bablokb/pcb-pico-datalogger/docs/pcb-datalogger-v2-2.jpg

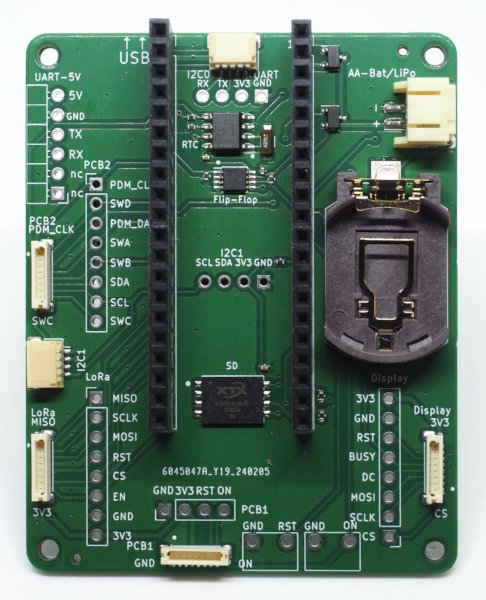
docs/pcb-datalogger-v2-2.jpg
