bablokb/pcb-pico-datalogger/docs/slim-case-v1-back.jpg

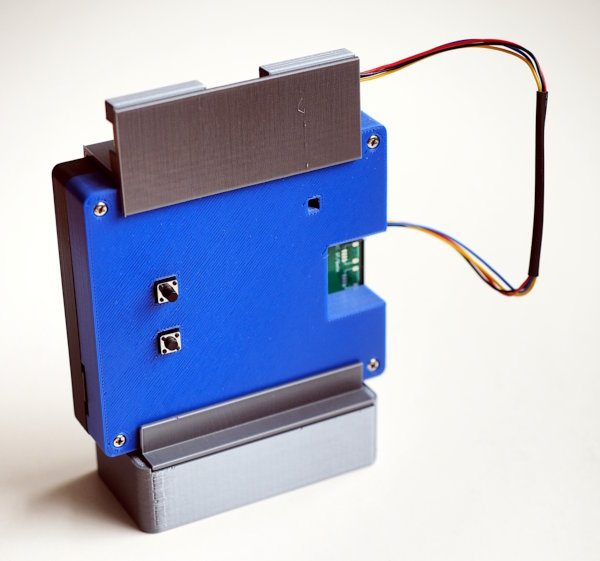
docs/slim-case-v1-back.jpg
