bablokb/pcb-pico-datalogger/docs/slim-case-v1-front.jpg

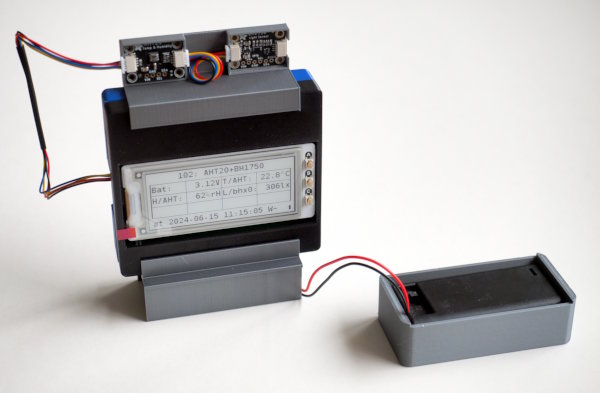
docs/slim-case-v1-front.jpg
