bablokb/pcb-pico-datalogger/lora-pcb.kicad/pcb-3D-top-JLCPCB.png

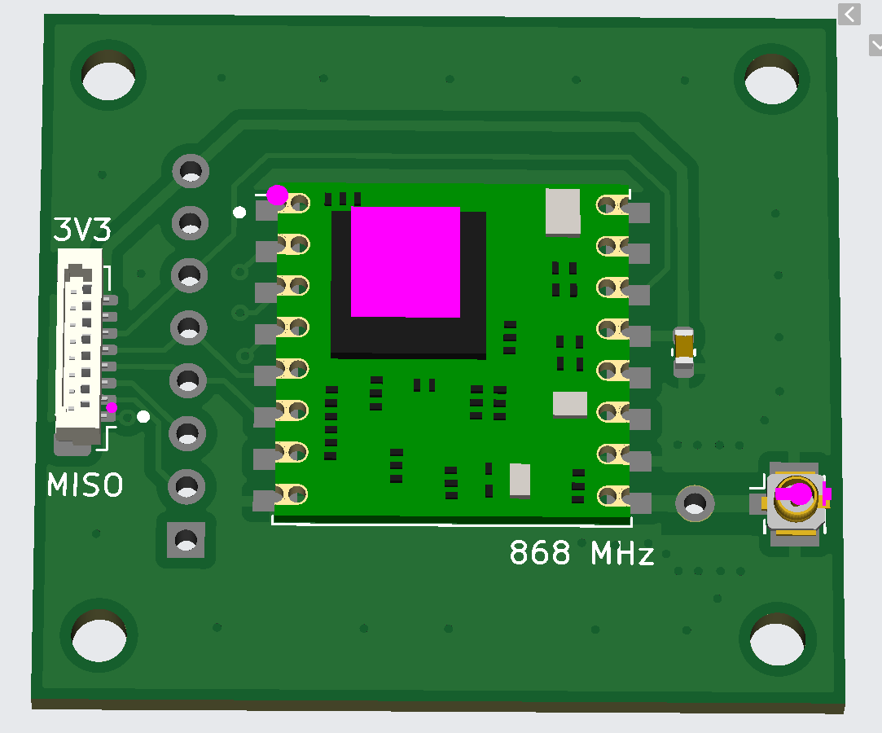
lora-pcb.kicad/pcb-3D-top-JLCPCB.png
