bablokb/pcb-pico-datalogger/src.shared/lora.py

#-----------------------------------------------------------------------------
# Setup of LoRa (adafruit_rfm9x.py). This class also encapsulates the
# data-protocol used by the dataloggers and gateway.
#
# Author: Bernhard Bablok
#
# Website: https://github.com/pcb-pico-datalogger
#-----------------------------------------------------------------------------

from log_writer import Logger
g_logger = Logger()

from singleton import singleton

from digitalio import DigitalInOut, Direction, Pull
import struct
import time
import adafruit_rfm9x
import pins

# --- quality of service settings   ------------------------------------------

# tuple of spreading-factor, coding-rate, signal-bandwidth
# Time per symbol is T(s) = 2**SF/BW
_LORA_QOS = [
  ( 7, 5, 125000),      # 0
  ( 7, 7, 125000),      # 1
  ( 8, 7, 125000),      # 2, default
  ( 9, 7, 125000),      # 3
  (10, 5, 125000),      # 4
  (11, 5, 125000),      # 5
  (11, 8, 125000),      # 6
  (12, 6, 125000),      # 7
  ]
_LORA_QOS_DEF = 2  # 0 is library default

# --- helper class for LoRa   ------------------------------------------------

@singleton
class LORA:
  def __init__(self,config,spi):
    """ constructor """

    # Calling the constructor with None will return the singleton, if it
    # exists. If not, bail out: the app has to retry and provide all arguments.
    if config is None:
      raise ValueError("config is None")

    self._config = config
    self._trace = getattr(config,'LORA_TRACE',False)

    # technical settings (QOS-setting with possible overrides)
    qos  = getattr(config, 'LORA_QOS', _LORA_QOS_DEF)
    sf   = getattr(config, 'LORA_SF', _LORA_QOS[qos][0])
    cr   = getattr(config, 'LORA_CR', _LORA_QOS[qos][1])
    bw   = getattr(config, 'LORA_BW', _LORA_QOS[qos][2])
    g_logger.print(f"LoRa: QOS-parameter: {(sf,cr,bw)}")

    # calculate expected app-level byte-rate: R(B) = sf*(4/cr)*bw/2**sf/8
    self._byte_rate = sf*4/cr*bw/(1<<(sf+3))
    g_logger.print(f"LoRa: expected byte-rate: {self._byte_rate:0.1f} B/s")

    if hasattr(pins,'PIN_LORA_EN'):
      g_logger.print("LoRa: enabling rfm9x")
      pin_enable = DigitalInOut(pins.PIN_LORA_EN)
      pin_enable.direction  = Direction.OUTPUT
      pin_enable.value = 1

    g_logger.print("LoRa: initializing rfm9x")
    pin_cs     = DigitalInOut(pins.PIN_LORA_CS)
    pin_reset  = DigitalInOut(pins.PIN_LORA_RST)
    self.rfm9x = adafruit_rfm9x.RFM9x(
      spi, pin_cs,pin_reset,config.LORA_FREQ,baudrate=100000)

    g_logger.print("LoRa: configuring rfm9x")
    self.rfm9x.spreading_factor = sf
    self.rfm9x.coding_rate      = cr
    self.rfm9x.signal_bandwidth = bw
    if (cr/4)* 1000 / (bw/(1 << sf)) > 16:
      self.rfm9x.low_datarate_optimize = 1
    else:
      self.rfm9x.low_datarate_optimize = 0

    self.rfm9x.enable_crc = True
    self.rfm9x.receive_timeout = getattr(config,'LORA_RECEIVE_TIMEOUT',5.0)
    self.rfm9x.tx_power = getattr(config,"LORA_TX_POWER",13)
    self.rfm9x.node = config.LORA_NODE_ADDR                      # this
    self.rfm9x.destination = getattr(config,"LORA_BASE_ADDR",0)  # gateway
    self.rfm9x.sleep()

  # --- trace LoRa-events   --------------------------------------------------

  def trace(self,msg):
    """ trace LoRa events """
    if self._trace:
      g_logger.print(msg)

  # --- transmit command   ---------------------------------------------------

  def transmit(self,data,msg_type=None,keep_listening=False):
    """ send data """
    if data is None or isinstance(data,str):
      if msg_type and data:
        payload = f"{msg_type},{data}"
      elif msg_type:
        payload = msg_type
      else:
        payload = data
      payload = bytes(payload, "UTF-8")
    else:
      # binary data has no message-type
      payload = data
    self.rfm9x.xmit_timeout = 2 + (len(payload)+4)/self._byte_rate
    if self._trace:
      g_logger.print(f"LoRa: sending data: {payload}")
      g_logger.print(f"LoRa:   xmit_timeout: {self.rfm9x.xmit_timeout: 0.1f}")
      start = time.monotonic()
    rc = self.rfm9x.send(payload,keep_listening=keep_listening)
    if self._trace:
      g_logger.print(f"LoRa:   elapsed: {time.monotonic()-start:0.3f}s")
    return rc

  # --- receive command   ----------------------------------------------------

  def receive(self, decode=True, keep_listening=True, timeout=None):
    """ receive and decode data """
    if self._trace:
      g_logger.print("LoRa: receiving data...")
      start = time.monotonic()
    packet = self.rfm9x.receive(with_header=True,
                                keep_listening=keep_listening,
                                timeout=timeout)
    if self._trace:
      g_logger.print(f"LoRa:   elapsed: {time.monotonic()-start:0.3f}s")
    if packet is None:
      self.trace(
        f"LoRa: no packet within {timeout if timeout else self.rfm9x.receive_timeout:5.2}s")
      return (None,None,None,None)
    else:
      header  = packet[:4]
      if decode:
        try:
          payload = packet[4:].decode()
        except Exception as ex:
          g_logger.print(f"exception while decoding packet: {ex}")
          return (None,None,None,None)
      else:
        payload = packet[4:]
      self.trace(f"LoRa: header: {header}")
      self.trace(f"LoRa: payload: {payload}")
      return (payload,int(header[1]),self.rfm9x.last_snr,self.rfm9x.last_rssi)

  # --- set destination   ----------------------------------------------------

  def set_destination(self,dest):
    """ set destination for transmit """
    self.rfm9x.destination = dest

  # --- broadcast a packet and wait for response   ---------------------------

  def broadcast(self,nr):
    """ send a broadcast packet to the gateway """

    # convert time (int) to compact hex-repr
    ts = time.time()
    ts_str =''.join([hex(b)[-2:] for b in struct.pack("i",ts)])

    # send packet ("B",TS,ID,nr)
    g_logger.print(f"LoRa: broadcast packet {nr}: sending at {ts}")
    start = time.monotonic()
    if self.transmit(
      f"{ts_str},{self._config.LOGGER_ID},{nr}", msg_type="B",
      keep_listening=True):
      duration = time.monotonic()-start
      g_logger.print(f"LoRa: broadcast: packet {nr}: transfer-time: {duration}s")
    else:
      g_logger.print(f"LoRa: broadcast: packet {nr}: failed")
      return None

    # wait for response
    return self.receive(keep_listening=False)

  # --- query time   ---------------------------------------------------------

  def get_time(self,retries=3):
    """ send a time-query packet to the gateway """

    for i in range(retries):
       # send packet ("T")
       g_logger.print(f"LoRa: sending time-query packet, retry={i}")
       start = time.monotonic()
       if self.transmit(None, msg_type="T", keep_listening=True):
         duration = time.monotonic()-start
         g_logger.print(f"LoRa: time-query {i} sent in {duration}s")
       else:
         g_logger.print(f"LoRa: : time-query {i} failed")
         continue

       # wait for response (binary)
       new_time = self.receive(decode=False, keep_listening=False)[0]
       if new_time:
         new_time,*_ = struct.unpack("i", new_time)
         g_logger.print(f"LoRa: : time-query {i} returned {new_time}")
         return new_time
    # query failed!
    g_logger.print(f"LoRa: time-query failed after {retries} retries")
    return None

  # --- send S-message   -----------------------------------------------------

  def send_single(self, data):
    """ send a single-line packet to the gateway """

    content_length = len(data)
    g_logger.print(f"LoRa: sending S-msg, length: {content_length}")
    if self.transmit(data, msg_type="S"):
      resp = self.receive(keep_listening=False, decode=False)
      if resp[0] and int.from_bytes(resp[0]) == content_length:
        g_logger.print("LoRa: ... successful")
        return True
      else:
        g_logger.print(f"LoRa: ... receive failed: response: {resp}")
        return False
    else:
      g_logger.print(f"LoRa: ... transmit failed")
      return False
