bablokb/pcb-pico-datalogger/src.shared/hw_helper.py

#-----------------------------------------------------------------------------
# Module with helper functions to setup the hardware. This module is
# reused by datacollector.py, admin.py, broadcast.py and gateway.py.
#
# Author: Bernhard Bablok
#
# Website: https://github.com/pcb-pico-datalogger
#-----------------------------------------------------------------------------

import atexit
import busio
import displayio
import sdcardio
import storage

from rtc_ext.ext_base import ExtBase

# --- atexit processing   ----------------------------------------------------

def at_exit_spi(spi,logger):
  """ release spi """
  try:
    # may fail if we want to log to SD
    logger.print(f"releasing {spi}")
  except:
    print(f"releasing {spi}")
  spi.deinit()

def at_exit_i2c(i2c,logger):
  """ release i2c-busses """
  try:
    # may fail if we want to log to SD
    logger.print(f"releasing {i2c}")
  except:
    print(f"releasing {i2c}")
  for bus in reversed(i2c):
    try:
      bus.deinit()
    except:
      pass

# --- initialize I2C-busses   ----------------------------------------------

def init_i2c(pins,config,logger):
  """ create and return list of I2C-busses """

  # Standard busses 0 and 1. Bus 0 is shared with UART, so we check
  # the configuration before creating it.
  try:
    i2c = [None,busio.I2C(pins.PIN_SCL1,pins.PIN_SDA1)]
    logger.print(f"created i2c1")
  except Exception as ex:
    logger.print(f"could not create i2c1: {ex}")
    i2c = [None,None]
  if config.HAVE_I2C0:
    try:
      i2c[0] = busio.I2C(pins.PIN_SCL0,pins.PIN_SDA0)
      logger.print(f"created i2c0")
    except:
      logger.print("could not create i2c0 although configured, check wiring!")

  # create busses behind a multiplexer
  if config.HAVE_I2C_MP:
    import adafruit_tca9548a
    for spec in config.HAVE_I2C_MP.split():
      name,loc = spec.rstrip(')').split('(')
      try:
        bus,addr = loc.split(',')
      except:
        bus = loc
        addr = '0x70'
      bus = i2c[int(bus)]
      addr = int(addr,16)
      if name[-2:] == '46' or name[-3:] == '46A':
        i2c_mp = adafruit_tca9548a.PCA9546A(bus,addr)
      else:
        i2c_mp = adafruit_tca9548a.TCA9548A(bus,addr)
      logger.print(f"adding {len(i2c_mp)} I2C-busses from {name}")
      for i2cbus in i2c_mp:
        i2c.append(i2cbus)

  # return result
  atexit.register(at_exit_i2c,i2c,logger)
  return i2c

# --- initialize SD-card   ---------------------------------------------------

def init_sd(pins,config,logger):
  """ initialize SD-card and return SPI-object """

  spi = None
  if config.HAVE_SD:
    try:
      spi    = busio.SPI(pins.PIN_SD_SCK,pins.PIN_SD_MOSI,pins.PIN_SD_MISO)
      sdcard = sdcardio.SDCard(spi,pins.PIN_SD_CS,1_000_000)
      vfs    = storage.VfsFat(sdcard)
      storage.mount(vfs, "/sd")
      logger.print("SD-card mounted on /sd")
      atexit.register(at_exit_spi,spi,logger)
    except Exception as ex:
      if spi:
        spi.deinit()
      raise
  return spi

# --- initialize RTC   -------------------------------------------------------

def init_rtc(pins,config,i2c):
  """ initialize RTC and return RTC-object """

  if config.HAVE_RTC:
    rtc_spec = config.HAVE_RTC.split('(')
    rtc_name = rtc_spec[0]
    rtc_bus  = int(rtc_spec[1][0])
  else:
    rtc_name = None
    rtc_bus  = 0

  # don't care about exceptions, must be handled by caller
  rtc = ExtBase.create(rtc_name,i2c[rtc_bus],net_update=config.NET_UPDATE)
  if rtc_name == "PCF8523":
    if pins.PCB_VERSION > 0:
      rtc.rtc_ext.high_capacitance = True  # uses a 12.5pF capacitor
    if config.HAVE_LIPO:
      rtc.rtc_ext.power_managment = 0b001  # direct switchover Vdd<Vbat
    else:
      rtc.rtc_ext.power_managment = 0b000  # Vdd<Vbat and Vdd < Vth
  return rtc

# --- initialize OLED   ------------------------------------------------------

def init_oled(i2c,config,logger):
  """ init OLED display """

  if config.HAVE_OLED:
    try:
      from oled import OLED
      odisp = OLED(config,i2c,logger)
      display = odisp.get_display()
      logger.print(
        f"OLED created with size {display.width}x{display.height}")
      return odisp
    except Exception as ex:
      logger.print(f"could not initialize OLED: {ex}")
      raise
  return None
