bablokb/pcb-pico-datalogger/src.shared/safemode.py

#-----------------------------------------------------------------------------
# Handle fatal exceptions.
#
# Author: Bernhard Bablok
#
# Website: https://github.com/pcb-pico-datalogger
#-----------------------------------------------------------------------------

import time
import board
import storage
import supervisor
import microcontroller
import pins
import hw_helper

from log_writer import Logger
g_logger = Logger('/sd/safemode.log')

try:
  import config
  TEST_MODE = config.TEST_MODE
except:
  TEST_MODE = False

# --- configure hardware   ---------------------------------------------------

if not hw_helper.init_sd(pins,config,g_logger):
  # no way to log anything, just reset
  microcontroller.reset()

try:
  i2c = hw_helper.init_i2c(pins,config,g_logger)
  the_rtc = hw_helper.init_rtc(pins,config,i2c)
  ts = the_rtc.print_ts(the_rtc.rtc_ext.datetime)
except:
  ts = "???"

reason = (f"{supervisor.runtime.safe_mode_reason}").split(".")[-1]
g_logger.print(f"safemode at {ts} with reason: {reason}")
microcontroller.reset()
