bablokb/pcb-pico-datalogger/src.shared/log_writer.py

#-----------------------------------------------------------------------------
# This class implements a singleton for logging. The constructor takes
# a single argument:
#
#   - None: don't print logmessages
#   - 'console': use normal print-statements for logging
#   - logfile: log to logfile 
#   - uart: an uart-object to receive the log statements
#   - in case of exceptions the latter two fall back to normal print output
#
# Note: this is a singleton, i.e. the logger is only configured the
#       very first time the constructor is called. This should be done
#       early in the (main) program.
#
# Author: Bernhard Bablok
#
# Website: https://github.com/pcb-pico-datalogger
#-----------------------------------------------------------------------------

import time
import supervisor
from singleton import singleton

MAX_CONSOLE_WAIT = 5

@singleton
class Logger():
  def __init__(self,target=None):
    """ constructor: save debug-target """
    self.set_target(target)

  def set_target(self,target=None):
    """ set target """
    self._target = target
    if target is None:
      self._print = lambda x: None
    elif isinstance(target,str):
      if target == 'console':
        self._print = self._print_to_console
        start = time.monotonic()
        while not (supervisor.runtime.serial_connected or
                   time.monotonic()-start > MAX_CONSOLE_WAIT):
          time.sleep(0.1)
      else:
        self._print = self._log_to_sd
    else:
      self._print = self._log_to_uart

  def print(self,msg):
    """ add timestamp and delegate to correct method """

    ts = time.localtime()
    ts_str = ("[%04d-%02d-%02d %02d:%02d:%02d]" %
              (ts.tm_year,ts.tm_mon,ts.tm_mday,
               ts.tm_hour,ts.tm_min,ts.tm_sec)
    )
    self._print(f"{ts_str} {msg}")

  def _print_to_console(self,msg):
    """ print to console """
    print(msg)

  def _log_to_sd(self,msg):
    """ write log to file """
    try:
      with open(self._target, "a") as f:
        f.write(f"{msg}\n")
    except:
      print(msg)

  def _log_to_uart(self,msg):
    """ write log to uart """
    try:
      self._target.write(bytes(f"{msg}\r\n",'utf-8'))
    except:
      print(msg)
