bablokb/pcb-pico-datalogger/src/tasks/send_udp.py

#-----------------------------------------------------------------------------
# Task: send data using UDP
#
# Author: Bernhard Bablok
#
# Website: https://github.com/pcb-pico-datalogger
#-----------------------------------------------------------------------------

from log_writer import Logger
g_logger = Logger()

from wifi_impl_builtin import WifiImpl
from secrets import secrets

def run(config,app):
  """ send data using UDP """
  wifi = WifiImpl()
  g_logger.print("UDP: sending data...")
  wifi.sendto(bytes(app.record+'\n',"UTF-8"),secrets.udp_ip,secrets.udp_port)
