bablokb/pcb-pico-datalogger/tools/show_sd.py

#-----------------------------------------------------------------------------
# Show contents of SD-card from the REPL.
#
# Run "from tools import show_sd" and then one of the commands printed.
# 
#
# Author: Bernhard Bablok
#
# Website: https://github.com/pcb-pico-datalogger
#-----------------------------------------------------------------------------

import atexit
import busio
import pins
import storage
import sdcardio
import os

# --- atexit processing   ----------------------------------------------------

def at_exit(spi):
  """ release spi """
  print(f"releasing {spi}")
  spi.deinit()

# --- helper methods   -------------------------------------------------------

def dump_file(name):
  with open(f"/sd/{name}","rt") as file:
    print(file.read())

def del_file(name):
  os.remove(f"/sd/{name}")

# --- main program   ---------------------------------------------------------

spi = busio.SPI(pins.PIN_SD_SCK,pins.PIN_SD_MOSI,pins.PIN_SD_MISO)
sdcard = sdcardio.SDCard(spi,pins.PIN_SD_CS)
vfs    = storage.VfsFat(sdcard)
storage.mount(vfs, "/sd")
print("SD-card mounted on /sd")
atexit.register(at_exit,spi)

csv = os.listdir("/sd")

print("files on /sd:")
for f in csv:
  print(f"   {f}")

print("\nexample usage:\n")
print("  show_sd.dump_file('message.log')")
print("  show_sd.dump_file('abc.csv')")
print("  show_sd.del_file('abc.csv')\n")
